Curiosity2611/Logic_Board_1/Logic_Board_1A/LB1A_DCA7M4_R512MB_F4GB/Design_Files/Kicad_Project/Rev1.0.0/STM32MP15xx_MPU.sch

## KiCad design Logic_Board_1A/LB1A_DCA7M4_R512MB_F4GB/Design_Files/Kicad_Project/Rev1.0.0/STM32MP15xx_MPU.sch (2021-05-28)

Schematic: STM32MP15xx_MPU.sch

Parts:
C1, C2, C5, C6, C63, C64, C65, C66, C67, C68, C69, C70, C72, C73, C74: 1uF; C_0402_1005Metric
C3, C4, C8: 100nF; C_0402_1005Metric
C7: 10nF; C_0402_1005Metric
C75, C76, C77: 10pF; C_0402_1005Metric
R1: 240E; R_0402_1005Metric
R2, R3, R4, R5: 1k5; R_0402_1005Metric
R6, R46: 10k; R_0402_1005Metric
R7: 3k; R_0402_1005Metric
U1: STM32MP157CAC3
X1: 32.768kHz; SiT1533AC-H5-DCC-32.768E
X2: 24MHz; TSX3225240000MF10ZC3

Notes on the sheet:
To PMIC
See Note: 1
See Note: 2
Notes
1. Used for PMIC & USB-C
2. Used for DSI, HDMI & RPi Header
STM32MP157CAC3 MPU
